sahilmuzkanti-afk/Mykeyboard/IMAGES/BOTTOM.png

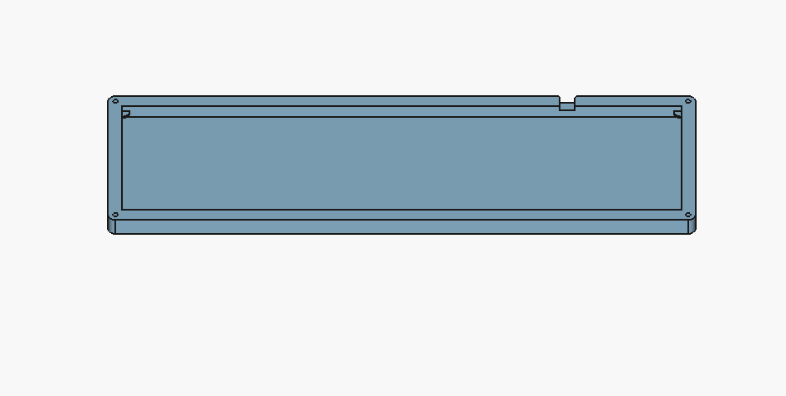
IMAGES/BOTTOM.png
