sahilmuzkanti-afk/Mykeyboard/IMAGES/DRC ( 0 ERROR ).png

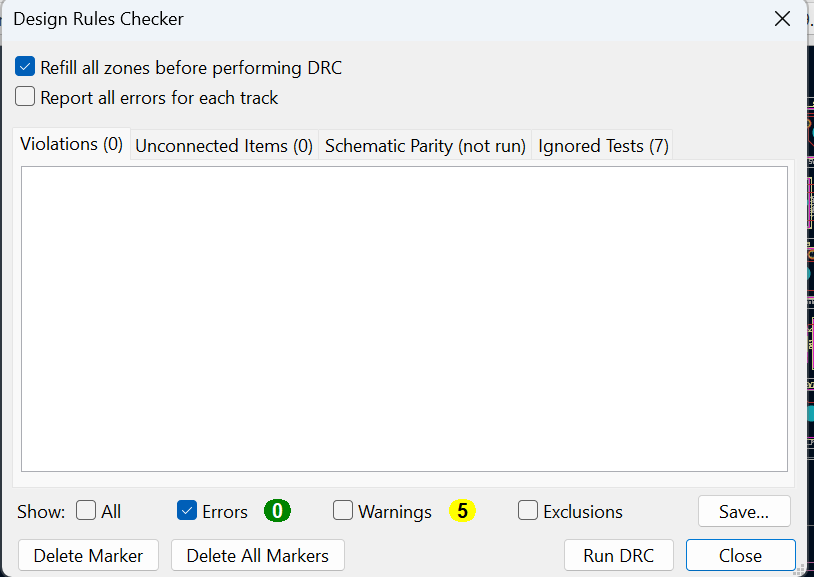
IMAGES/DRC ( 0 ERROR ).png
