sahilmuzkanti-afk/Mykeyboard/IMAGES/ASSEMBLY 2nd angle.png

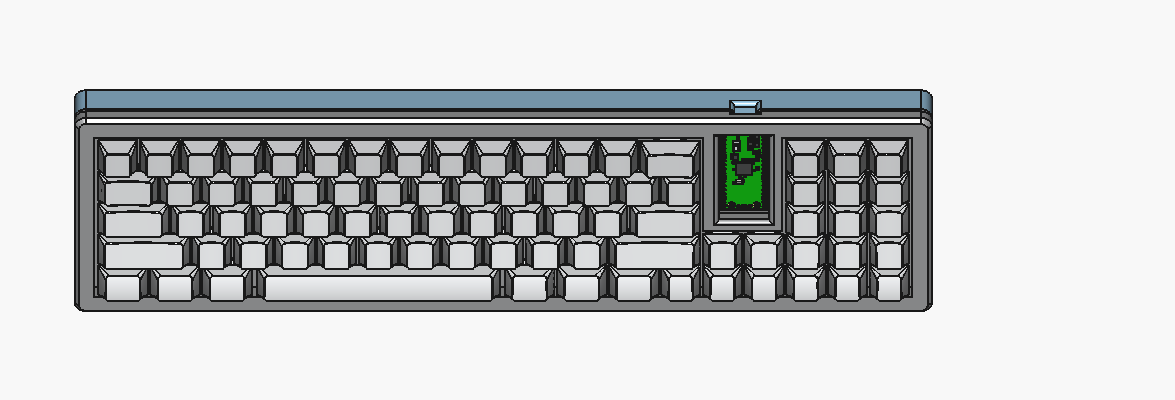
IMAGES/ASSEMBLY 2nd angle.png
