sahilmuzkanti-afk/Mykeyboard/IMAGES/ASSEMBLY.png

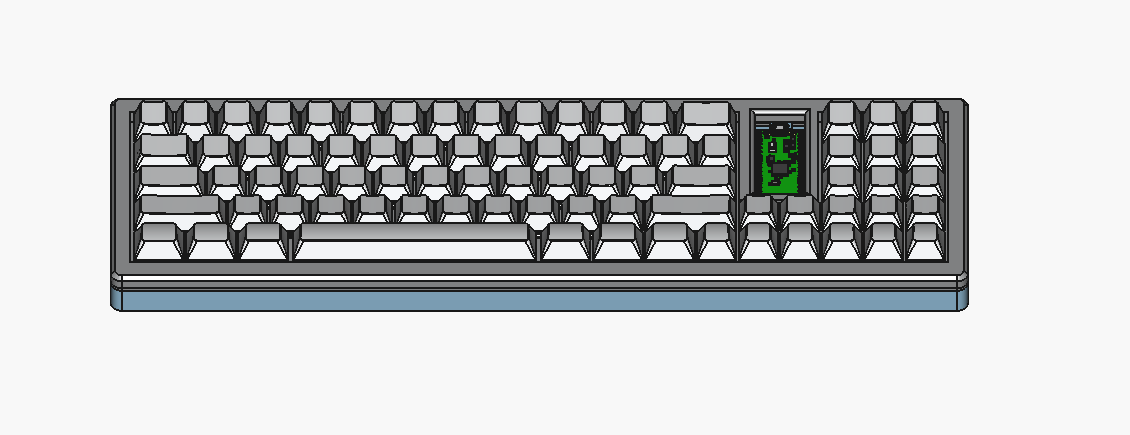
IMAGES/ASSEMBLY.png
