sahilmuzkanti-afk/Mykeyboard/IMAGES/PCB STEP.png

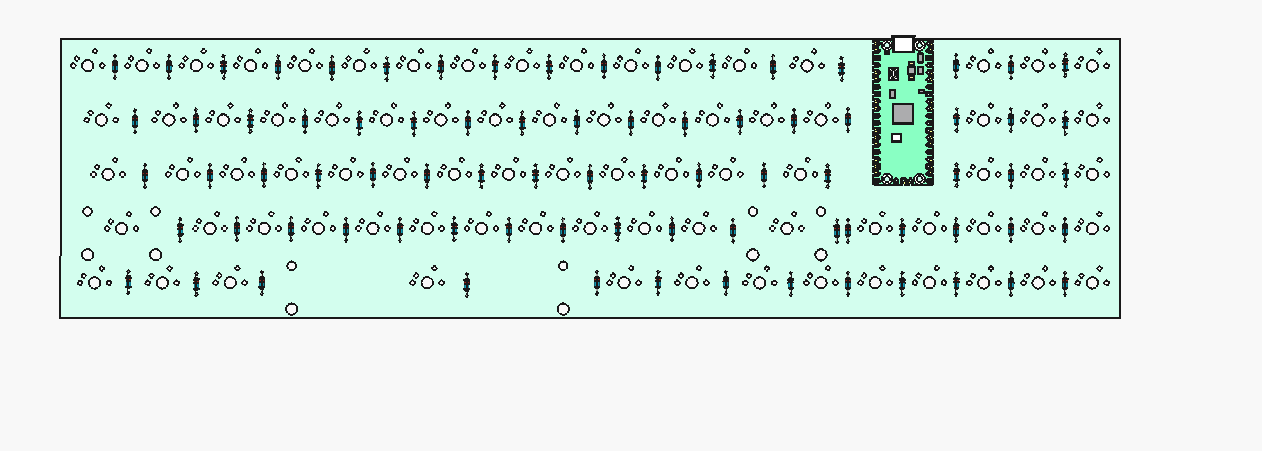
IMAGES/PCB STEP.png
